WhenLifeHandsYouLemons/LED-Light-Wall/assets/img/fullsize/others/others-1.jpg

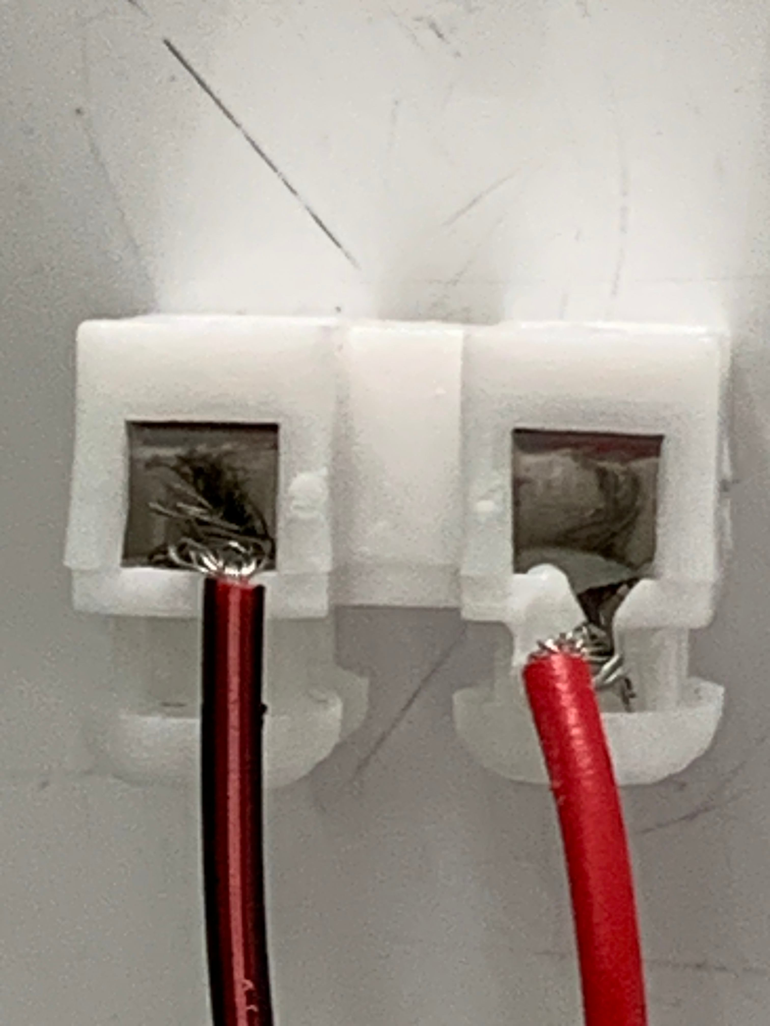
assets/img/fullsize/others/others-1.jpg
