WhenLifeHandsYouLemons/LED-Light-Wall/assets/img/fullsize/others/others-2.jpg

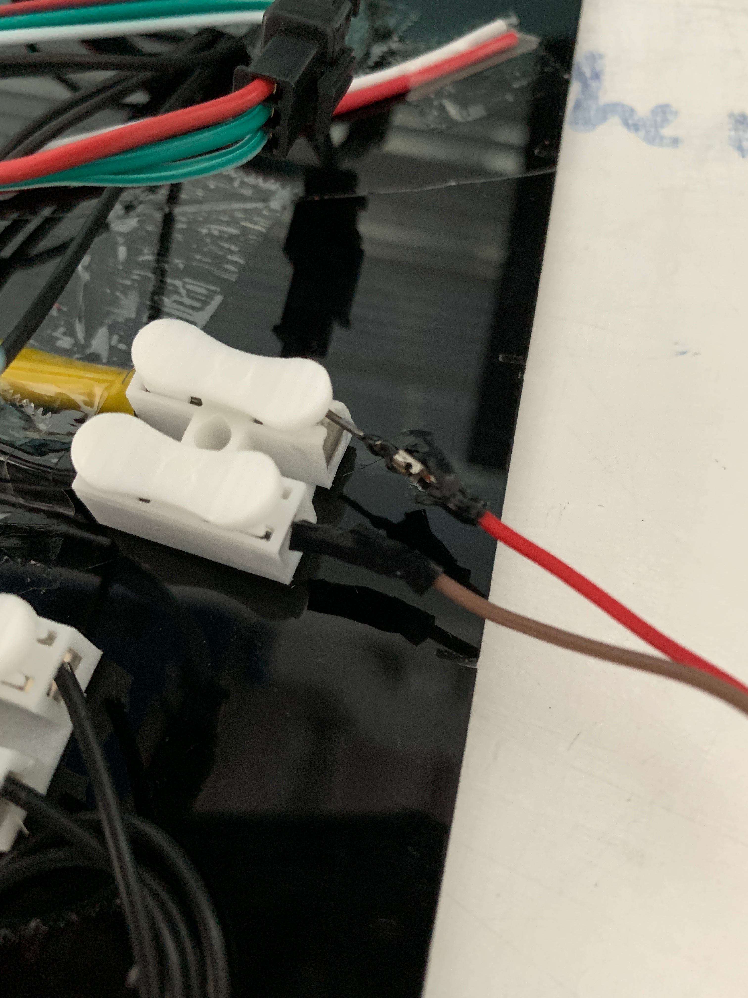
assets/img/fullsize/others/others-2.jpg
