WhenLifeHandsYouLemons/LED-Light-Wall/assets/img/fullsize/v2/designs/designs-1.jpg

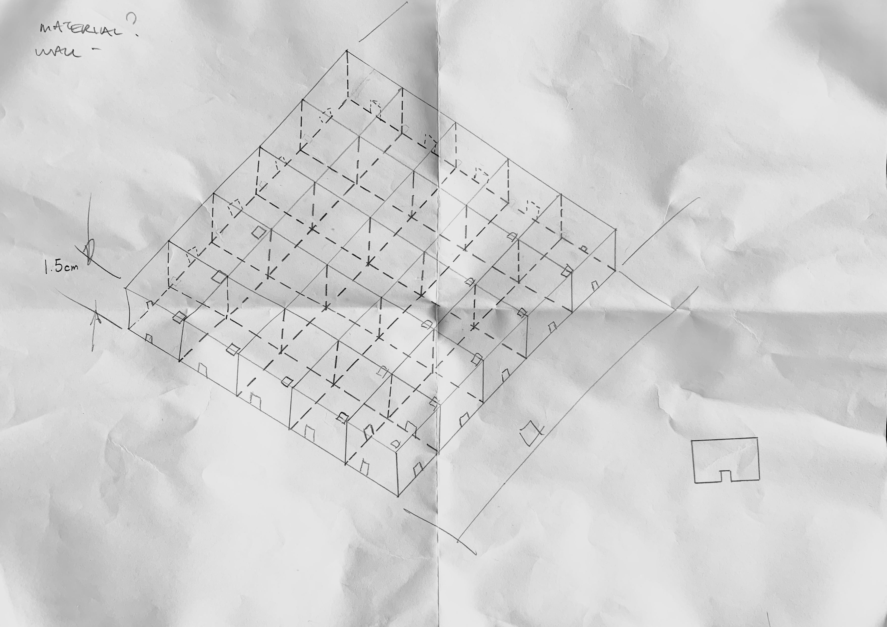
assets/img/fullsize/v2/designs/designs-1.jpg
