WhenLifeHandsYouLemons/LED-Light-Wall/assets/img/fullsize/v2/designs/designs-6.png

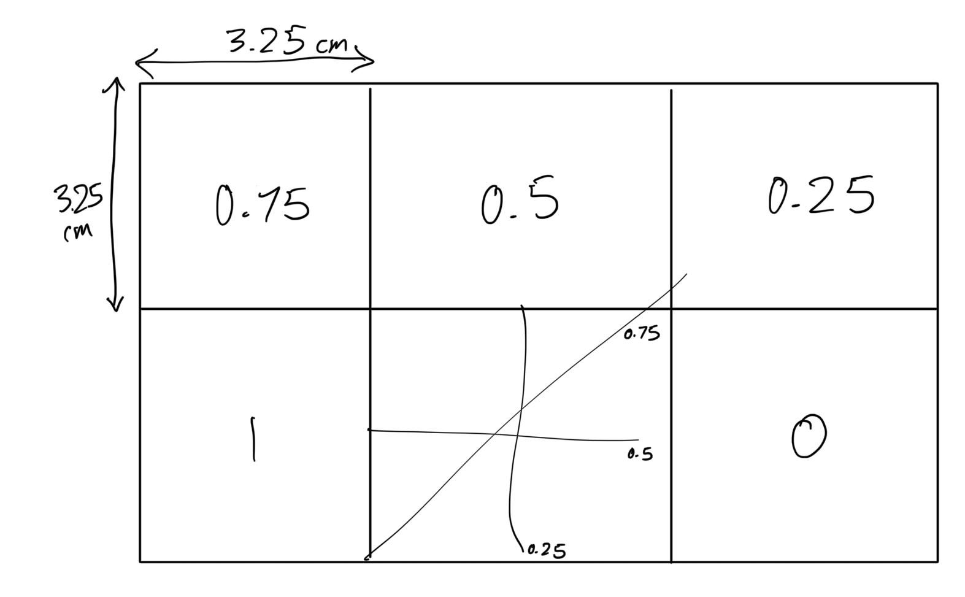
assets/img/fullsize/v2/designs/designs-6.png
