WhenLifeHandsYouLemons/LED-Light-Wall/assets/img/fullsize/v2/photos/photos-3.jpg

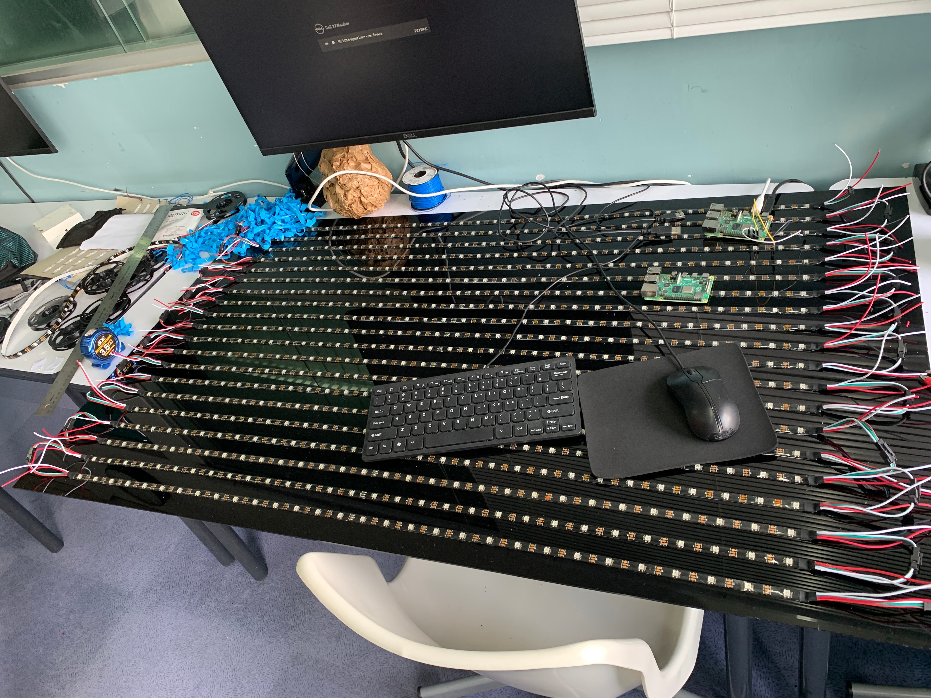
assets/img/fullsize/v2/photos/photos-3.jpg
