WhenLifeHandsYouLemons/LED-Light-Wall/assets/img/fullsize/v2/photos/photos-6.jpg

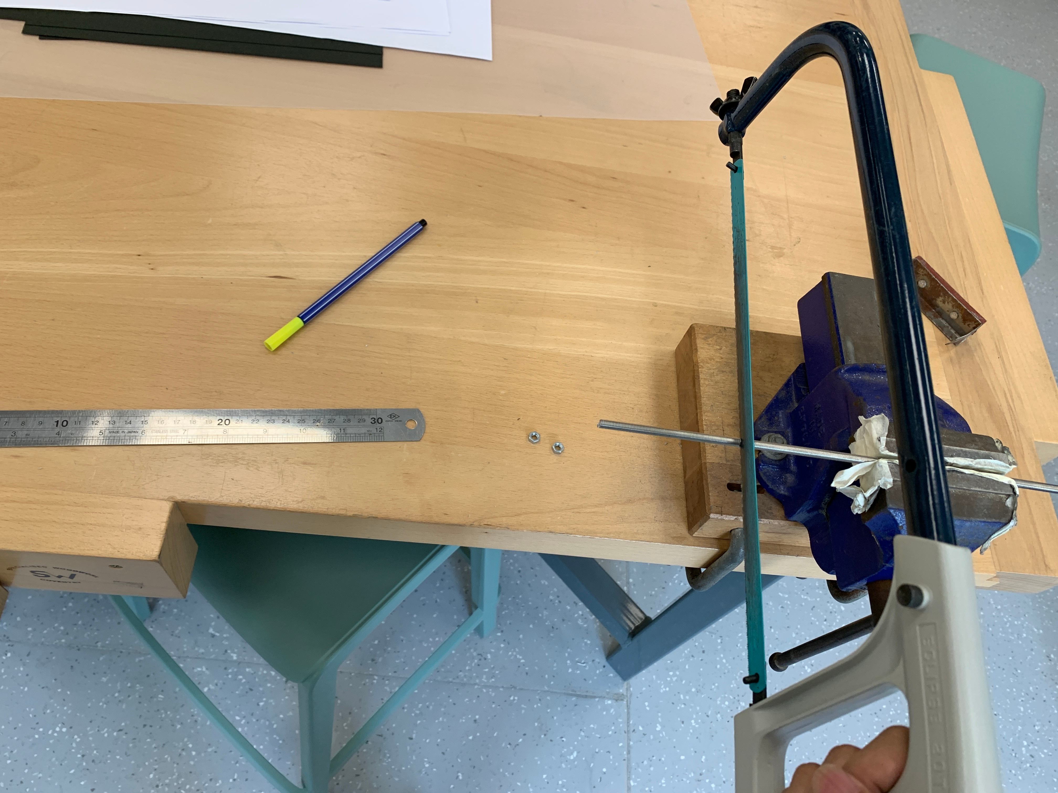
assets/img/fullsize/v2/photos/photos-6.jpg
