WhenLifeHandsYouLemons/LED-Light-Wall/assets/img/fullsize/v2/photos/photos-9.jpg

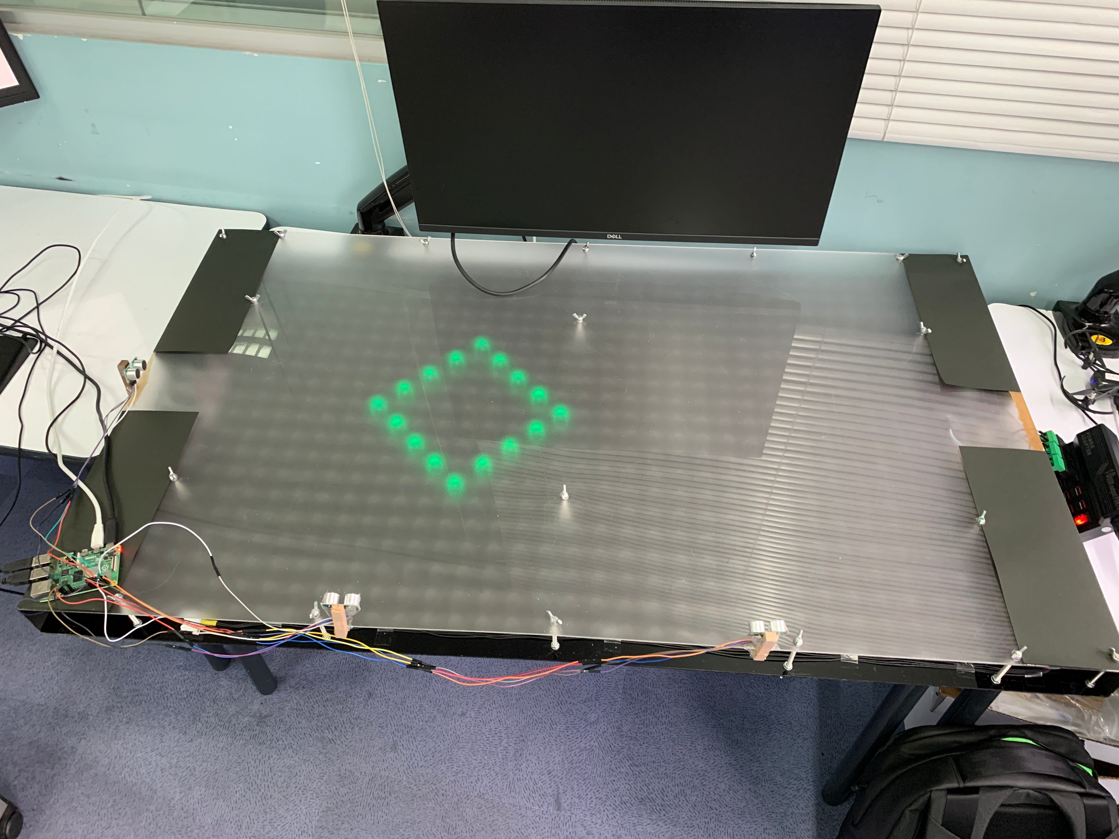
assets/img/fullsize/v2/photos/photos-9.jpg
