WhenLifeHandsYouLemons/LED-Light-Wall/assets/img/fullsize/v2/renders/renders-1.jpg

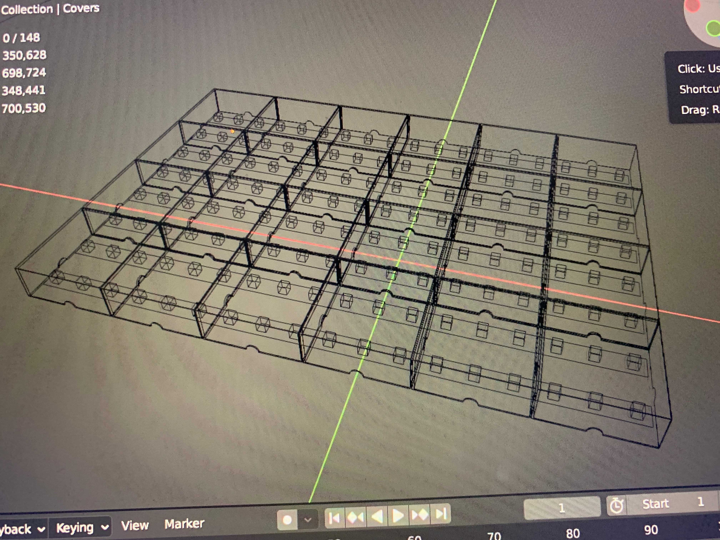
assets/img/fullsize/v2/renders/renders-1.jpg
