WhenLifeHandsYouLemons/LED-Light-Wall/assets/img/fullsize/v2/renders/renders-7.png

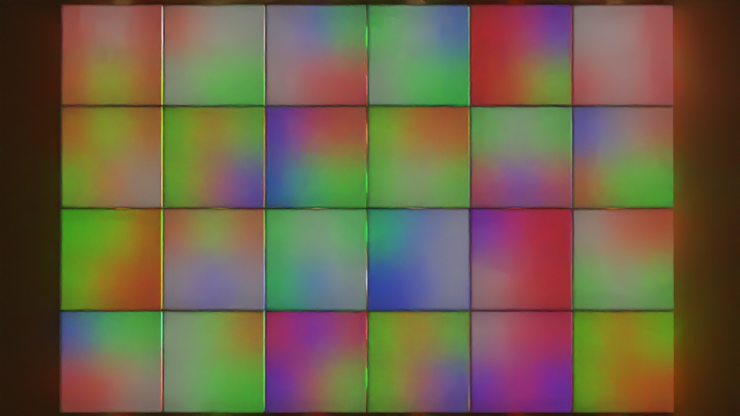
assets/img/fullsize/v2/renders/renders-7.png
