WhenLifeHandsYouLemons/LED-Light-Wall/assets/img/thumbnails/v2/renders/renders-2.jpg

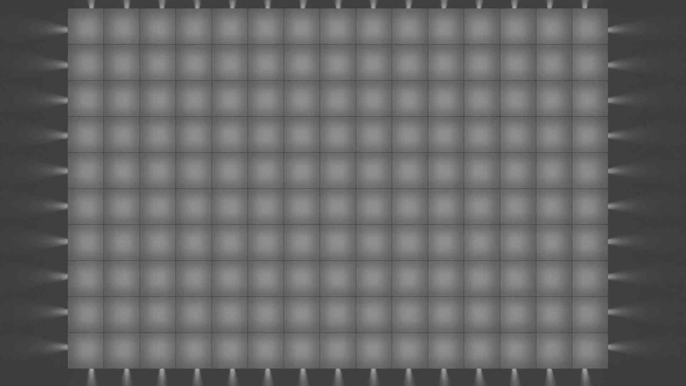
assets/img/thumbnails/v2/renders/renders-2.jpg
