WhenLifeHandsYouLemons/LED-Light-Wall/assets/img/thumbnails/v2/renders/renders-3.jpg

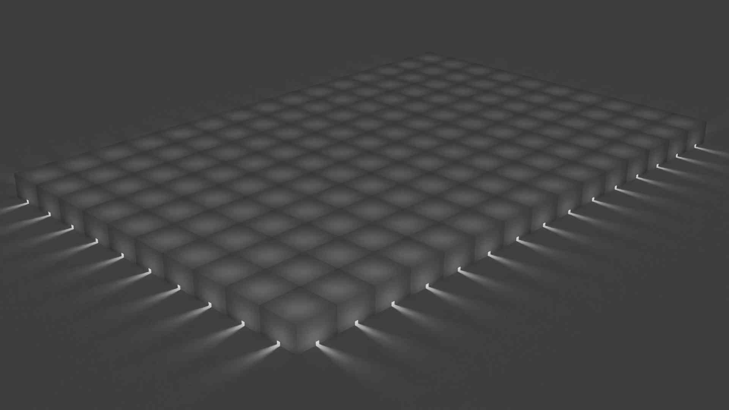
assets/img/thumbnails/v2/renders/renders-3.jpg
