WhenLifeHandsYouLemons/LED-Light-Wall/assets/img/thumbnails/v2/renders/renders-5.jpg

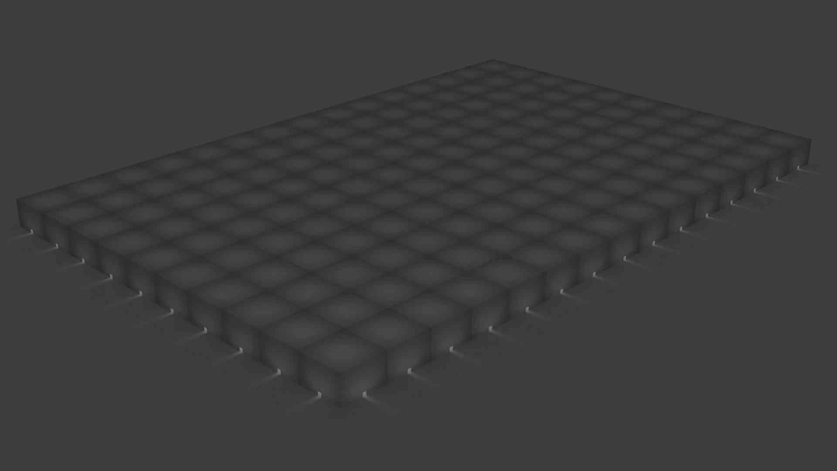
assets/img/thumbnails/v2/renders/renders-5.jpg
