WhenLifeHandsYouLemons/LED-Light-Wall/Others/warning_sticker_v1.png

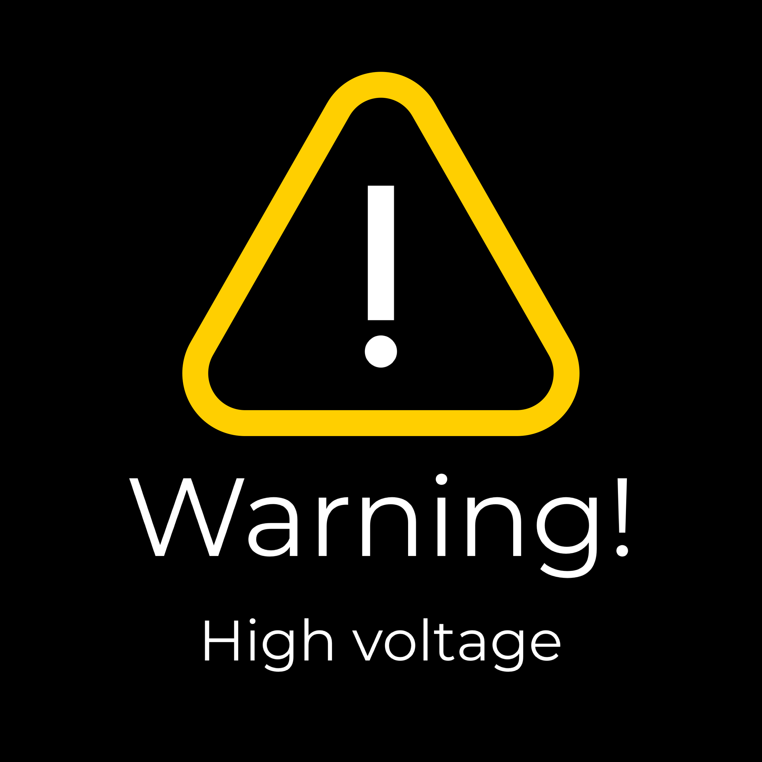
Others/warning_sticker_v1.png
