WhenLifeHandsYouLemons/LED-Light-Wall/assets/img/fullsize/v2/mat_test/mat_test-5.jpg

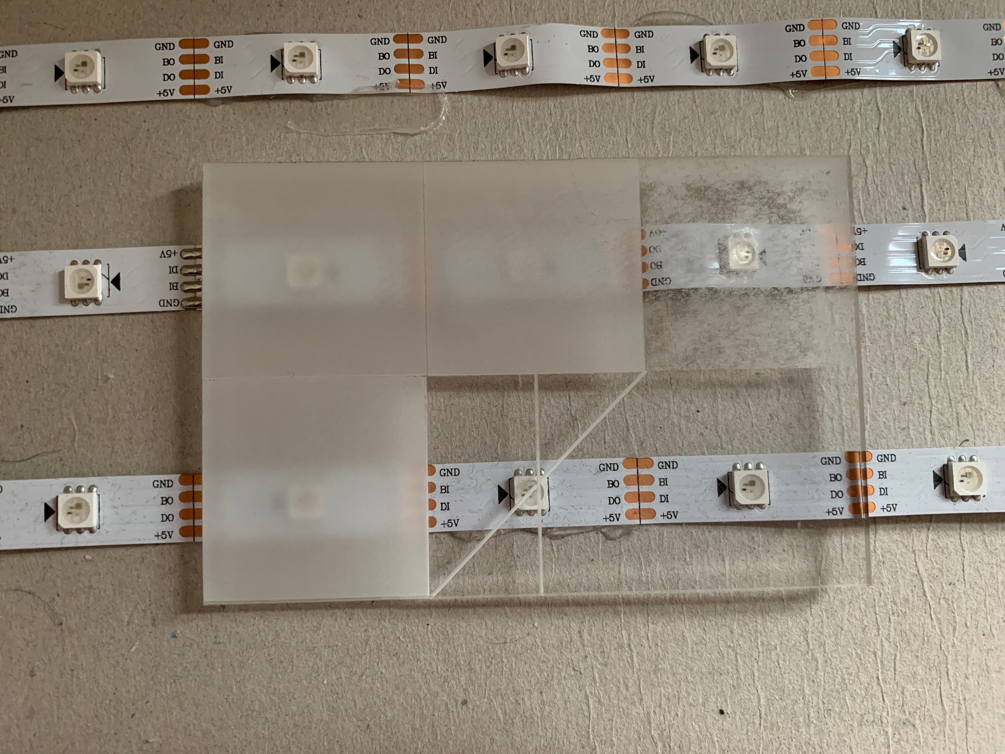
assets/img/fullsize/v2/mat_test/mat_test-5.jpg
